gkoh/pico-cec/openscad/pico-cec-top.scad

include <pico-cec-lib.scad>

top();
